John-ODell/Make_Music/hardware/review/final-package-20261009/before-corrections-REVIEW.md

# Final held-package review — 2026-10-09

Reviewed package commit d987896dbdd8cb6059bc102323f3ea0d89e263e1, root head23a23b6237898ece736c14430cfd86f4a77c5c58. The two later commits change checkpoint documentation; manufacturing payload and native CAD match the reviewed package. No repository/CAD/config writes, editor operations, exports, supplier contact/upload/order or merge occurred. Evidence was read from native exports and the source-bound recorded MCP results; no new live state or physical test is claimed.

## Verdict

No electrical, sourcing, placement or hash blocker was found. PR28 is suitable to merge **as a held review project after the ordinary package-presentation and parity-prose corrections below**. This is not a fabrication or upload release. Root owns corrections, regenerated manifest and merging.

## Verified

- All24 manifest input and65 output SHA256 values match; complete on-disk coverage is66 files including manifest. All17 native design/library hashes equal21b2108. Copies of README, assembly handoff and instrument-parts match their recorded inputs.
- Circuit contract and recorded IPC evidence agree on166 pads,48 values/full footprint IDs,65 footprints,38 connected nets and6 NC nets. U2 ten role/type assignments, power separation, cable/pull-up/bypass contracts and native MPNs pass. Identity sync is noop.
- Recorded saved/refilled all-severity ERC0, copper/layout DRC0, unconnected0; exactly4 reviewed metadata warnings, not suppressed. Native schematic parity count is4; electrical/net/value/full-ID discrepancy count is0. These are different categories.
- All47 purchased BOM refs/MPNs/values/footprints/datasheets match native XML. All47 native placement rows match recorded IPC x/y, rotation, side, value and footprint, including30 top SMT and17 THT with H1 underneath. Both derived placement tables agree. Five-unit sourcing fields and quantities expand exactly to235 carrier parts; optional bare carrier is separate.
- Generator diff from21b2108 changes only csv.DictWriter lineterminator to LF. A temporary quoted/comma/embedded-newline CSV round-trip passed; no CAD behavior change. Do not regenerate CAD to resolve these document issues.
- Package README, validation flags and visual-review scope preserve exact-part fit, long18650/holder/charger, final mechanical CAD, factory process and first-article/all-five bench holds. PM's actual Gerber/detail and five native drawing-page inspections are source-hashed recorded evidence; they were not visually rerun here.

## Corrections before final held-review merge

1. **Grouped connector descriptions (P2):** prepare_pcbway_review.py187 copies the first reference's functional Value into a group whose key excludes Value. In pcbway-bom-five.csv, J1/J2 are both labeled LEFT/Pico1–20 and J3–J14 all C4/GP16. Sourcing identities and per-reference carrier-bom are correct, but the group description falsely assigns one function to all references. Use a generic physical-part description for mixed-function groups, or split grouping by Value. Regenerate ordinary BOM/manifest and verify all235 quantities remain correct.
2. **Copied handoff links (P2):** copying assembly/PCBWAY_HANDOFF.md into the held package without rebasing its relative links breaks six required references: MODULE_HARNESSES.md, FIT_CHECKLIST.md, mechanical BUILD_READINESS, paper-fit PDF, power prototype-validation and budget worksheet. Adjust links for repository/package context or bundle companion review documents and validate final destinations. Preserve their hold language.
3. **Parity taxonomy (P2):** WORK_CHECKPOINT.md23 says unconnected/parity0, but native schematic_parity_issues is4. Replace misleading prose and add explicit classified counts if useful; retain the four exact native warning records. Do not change rules or native fields to make a zero claim.

Independent machine-check results, exact alias mismatches and broken-link destinations are in results.json; connectivity command output is in connectivity-output.txt. These findings were sent to PM. No current package hash is stale at the frozen audit snapshot; root's forthcoming document/package corrections require a new manifest.
