John-ODell/Make_Music/hardware/review/prequote-20261009/electrical/REVIEW.md

# Final electrical team review before quote — 2026-10-09

**ACCEPTED for quote-only review of five complete factory instruments**, plus optional sixth bare carrier. No actionable new electrical finding. This is not fabrication readiness or permission to order/upload. Root handles the authorized quotation workflow.

Scope: root checkout `/Users/johnodell/Desktop/Make_Music`, exact merged commit07f0e03b4d69f809a0e0871b89afc9e052754bba. All17 native source/library hashes match21b2108 before/after; source snapshots are retained. Reviewed current package exports and source-bound recorded MCP evidence. No repository/CAD/library/config changes, sync, refill, GUI operation, export, supplier contact or upload occurred.

Fresh saved-file Konnect13.0/KiCad10.0.6 checks completed: full-severity ERC0; layout/copper DRC0; unconnected0; exactly4 retained native metadata parity warnings. C17/C18 missing Header and J1/J2 missing MPN descriptions/UUIDs exactly match the reviewed native records. No hidden category, truncation, rule suppression or metadata substitution. Fresh DRC explicitly reports saved_file, live_board_synced=false, zones_refilled=false. These checks do not claim a newly saved/refilled or freshly inspected live GUI state.

All166 source-bound recorded IPC pad nets,48 values/full footprint IDs and identity-sync noop agree with native XML. Circuit verifier checks38 connected nets/6 NC nets, all41 typed power endpoints, ten U2 terminals/no pad11, fused switched battery path and D2/D3 polarity, and separation of VBUS/battery/VSYS/3V3. All40 Pico socket physical positions/GPIO assignments use the previously independently verified unchanged mapping: J1.n=Pico n; J2.n=Pico n+20. Notes GP16–22/26, left semitone/octave GP27/28, J13/J14 signals GP13/12, and free GPIO0–11/14/15 remain correct.

Unchanged firmware uses both GP12/13 channels at the same frequency, HIGH idle for active-low ST0238, and per-touch active-level configuration. Existing host tests/mapping/circuit checker are unchanged from the reviewed revision; no redundant firmware test rerun or new hardware-performance claim. R1/R2 reset pull-ups and C11/C12/C17/C18 supply bypasses match the circuit. Carrier contact order1SIG/2regulated3V3/3GND requires the documented ST0238 GND/I/O/VCC permutation; actual module-end labels, polarity/momentary configuration and reset/sound behavior remain delivered-part/bench gates.

All47 native placements match recorded IPC x/y/rotation/side/value/footprint; correct BOM/functional descriptions cover47 unique purchased references and235 parts for five. Thirty top SMT/17THT with H1 beneath. Current assembly tables and electrical evidence are byte-identical to the accepted follow-up. Native parity4 remains separate from electrical discrepancy0. No sourcing/placement mismatch was found.

Exact Pico/socket/module/cell/holder fit, protected P1835J lot/terminal limits, L1 charger pairing hold, contact/crimp ampacity, final fixture/cassette CAD, factory land/stencil/annular-ring/panel/orientation acceptance, first-article/all-five bench and source-isolation/UVLO/fault/thermal tests remain open. Quote-only acceptance permits pricing/metrology/process discussion; it waives none of those release gates.

Results and full raw responses are in this directory. Review complete; idle after handoff.
