John-ODell/Make_Music/hardware/review/prequote-20261009/power/REVIEW.md

# Final power review for conditional quotation — 2026-10-09

Reviewed merged commit **07f0e03b4d69f809a0e0871b89afc9e052754bba** read-only. **Conditionally accepted for quote review; not ready for hardware fabrication.** No CAD/document/repository changes, new editor checks, supplier contact or upload were performed. All files produced by this helper are in this temporary review directory.

## Evidence checked

- Frozen merged packet inputs: **61 input hashes and 43 support-input hashes pass**, covering 63 unique source files. **109 packet output hashes**, all **17 native source hashes** across three matching source checkpoints and **128 package-local links** pass. Current rear-edge XML/ERC/DRC/live-board records match the packet copies. These are saved/source-bound evidence checks, not a new live ERC/DRC run.
- Recorded connectivity/board verification passes: **166 physical endpoints /48 electrical parts /41 power endpoints**, all pad nets/values/full footprint IDs agree; identity synchronization is a no-op. ERC0, copper/layout DRC0 and unconnected0; **four exact metadata/parity warnings remain**, so overall DRC/parity is not zero.
- All **47 purchased carrier references** match native MPN/value/footprint and recorded X/Y/rotation/side. **31 grouped sourcing rows /235 parts for five**, **30 top SMT /17 THT per carrier**, only **H1 bottom**; the SMT and manual-THT placement tables have exact coverage/coordinates.
- Exact power parts and orientation contract agree: **TPS259474LRPWR** U2 (ten terminals, IN5/OUT6, no pad11), **3403.0275.23** F1 upstream, **MN12SS1W03** S1 (common2/ON3/OFF1 NC), **SS14-E3/61T** D2 shunt K1 VSYS/A2 GND, **SMAJ5.0CA** D3 bidirectional input TVS, **B2B-PH-K-S(LF)(SN)** H1 positive1/GND2. No carrier series D1. USB uses the unmodified Pico's onboard diode; no raw-cell/USB connection to 3V3/GPIO. USB powers the instrument with S1 OFF, does not charge the cell and bypasses the battery F1/U2 protection.
- C17/C18 are **C2012X7R1A106K125AC**, 10µF each on regulated3V3/GND, retaining twelve100nF bypasses. C13/C14/C16 are **C2012X7R1E475K125AB** and C15 **C1608C0G1H103J080AA**. Main nominal VSYS subtotal remains56.4µF, separate from the additional20µF on3V3. Effective capacitance and startup remain unmeasured. Limits remain0.70A battery input,250mA external/350mA total3V3 and100µF maximum VSYS; the515mA low-voltage sizing example is not a measured load or runtime guarantee.

## Quote-document disposition

The merged07f0e03 request compared complete, SMT-only and bare routes. The newly authorized middle route must be **five carriers with all47 purchased parts soldered**, including all17THT parts and bottomH1: **150SMT +85THT parts for five**. Pico/modules/cell/holder/harness/mechanics/final instrument tests are explicit exclusions or separate lines for this middle route. SMT-only may remain an additional breakdown. These are alternatives for the same physical design, not fifteen ordered boards. The optional sixth bare keepsake is additional.

During the read-only audit, PM began that authorized ordinary-document update. Root HEAD remained 07f0e03, but live `hardware/assembly/QUOTE_REQUEST.md` changed; its **two manifest input entries differ** from the old packet. Its frozen 07f0e03 blob matches both recorded hashes. The observed new draft correctly adds the three requested alternatives and maintains quote-only authorization/production holds. PM subsequently updated `ASSEMBLY_BUDGET.md` with the same all-47 carrier option; the ordinary-document correction is complete in those live drafts. **Regenerate the coherent quote packet and manifest after final ordinary-document edits, then verify all inputs/outputs before quote submission.** This is expected document staleness during PM work, not a circuit-source defect. `packet-checks.json` retains the two live differences seen at that earlier instant; later budget edits add another input change. `frozen-input-checks.json` records the all-pass merged baseline.

## Remaining fabrication and first-article requirements

No new actionable circuit discrepancy was found within this source/export review. The following existing gates remain material and must accompany a conditional quote:

- Delivered **P1835J opposite-end button-top** identity, current-lot charge/discharge/PCM thresholds/recovery and measured holder fit/removal/retention. Published planning dimensions do not prove the exact variant fits.
- **External charger compatibility HOLD:** L1's4.242V upper tolerance exceeds the cell page's unqualified4.20V maximum. Selecting500mA or a shared brand does not approve pairing. Require current-lot CC/CV voltage/current/termination/temperature limits, accepted charger revision/tolerances/recovery and bay fit. One shared5V1A supply/cable/charger set is only a quote assumption; no approved pair or exact input-supply SKU exists.
- **BH-18650-W** contact/holder capability for0.70A normal and≥1.2A continuous branch; included factory24AWG TR64 leads150±5mm each, no duplicate wire purchase. Measure insulation OD against JST **0.8–1.5mm** and qualify **PHR-2 /SPH-002T-P0.5S** strip/tool/crimp, continuity, polarity, service bends and strain relief. Wire color and supplied stripped length are not qualification.
- Final measured/toleranced cassette/retention/support drawings and≥2mm loaded clearance; nominal112×36×44mm cassette and≥47mm supports remain proposals. Factory acceptance of U2 mask/stencil, capacitor lands, socket annular rings, panel rails/fiducials, orientation and handling remains open.
- Current-limited emulator bring-up before a real cell: measured load/current/thermal/startup, UVLO/restart, fault latch/reset/reversal/isolation, effective capacitors and switch low-load endurance. Separate USB source/inrush/fault qualification is required because USB bypasses F1/U2. Measured module operation/current and actual touch configuration remain pending.
- **First article within the five**, followed by separate acceptance records for **all five**; the optional bare board receives no populated-component allocation. No physical fit, bench result, supplier acceptance, price or fabrication release is claimed.

The packet's physical-fit, bench, supplier-acceptance and fabrication-release flags are all false. Conditional quote review may proceed after PM's coherent quote-document/package refresh; fabrication or first-article assembly requires its separate release gate.
