John-ODell/Make_Music/hardware/manufacturing/REVIEW_ONLY_DO_NOT_ORDER/support/hardware/mechanical/MODULE_FIXTURE.md

# Raised module fixture — dimensioned prototype proposal

Updated 2026-10-09 for the corrected 18650 cassette; upper-fixture geometry was reviewed 2026-10-08. Propose one machined **unfilled acetal insulating plate**, open-backed seats, and removable insulating edge keepers for all ten touch boards and both ST0238 boards. Nothing passes through a module's undocumented mounting holes. Module wiring uses flexible, factory-installed leads; headers and solder joints carry no playing load. This is an engineering fixture proposal, **not verified actual-part fit, a strength certification, or manufacturing CAD**.

The editable [plan and detail drawing](module-fixture-plan.svg) and [carrier attachment CSV](fixture-mounting.csv) define the proposal. PM owns PCB edits. Dimensions retain the legacy carrier service datum native (20,20): local (0,0), x right, y forward, millimetres. The PM's KiCad offset adds (20,20); both coordinate sets are in the CSV. For the proposed 330 x121.5 carrier the new physical rear edge is legacy y=-1.5/native y18.5, while every fixture/body/mount coordinate stays fixed. DATUMS.md distinguishes the physical upper-left from this retained service origin. z=0 is the carrier **top** surface, unlike the cassette document's underside z convention. Selected delivery is five complete instruments and an optional sixth bare carrier; the [physical-fit checklist](PHYSICAL_FIT_CHECKLIST.md) assigns metrology/assembly to the assembler and paper-fit/reach to the user.

## Geometry and fixed carrier interface

Plate perimeter polygon, in order: **(2,36), (42,36), (42,56), (120,56), (120,68), (326,68), (326,119), (2,119)**. Bounding size 324 x 83. Main plate thickness **4 mm**, raised on **24 mm** custom insulating spacers (OD8, ID3.2), giving a module support plane z=28. Machine integral 1 mm-high locating fence segments from a 5 mm blank; main plate/fastener seats remain 4 mm thick. Stock material, machining radii, flatness and tolerances need fabricator agreement. Do not use carbon-filled plastic or conductive coatings.

Nine **3.2 mm NPTH carrier and plate holes**, with **8 mm diameter copper/component keepouts on both carrier faces**:

| ID | Mechanical (x,y) | KiCad (x,y) |
|---|---|---|
| F1 | (8,74) | (28,94) |
| F2 | (45,83) | (65,103) |
| F3 | (50,114) | (70,134) |
| F4 | (155,114) | (175,134) |
| F5 | (257,114) | (277,134) |
| F6 | (291,114) | (311,134) |
| F7 | (155,73) | (175,93) |
| F8 | (189,73) | (209,93) |
| F9 | (291,73) | (311,93) |

These are additional to the four corner supports and four cassette mounts; do not share bolts with the removable cassette. Plate-only 8 mm tool-access openings at the two existing front carrier supports (6,114) and (324,114) preserve access; the right opening forms an edge notch. No extra carrier holes are required for these openings. The minimum fixture attachment centre-to-plate-edge distance is 5 mm, leaving at least 1 mm beyond the 4 mm keepout radius.

## Twelve seats and removable keepers

| Boards | Centre coordinates | Nominal PCB body | Proposed seat opening / corner ledges |
|---|---|---|---|
| Eight notes C4..C5 | x=70,104,138,172,206,240,274,308; y=94 | 24 x 24, user reference | 24.6 x 24.6, with four integral 3 x 3 corner tabs retained in that opening |
| Semitone / octave | (24,54), (24,94) | 24 x 24, user reference | Same touch seat |
| Buzzer 1 / 2 | **(60,67.5), (98,67.5)** | 32 x 14, ST0238 listing | 32.6 x 14.6, with four integral 5 x 3 corner tabs |

The buzzer bodies move 1 mm left and 4.5 mm forward from the earlier body reservation, independently of the PM's fixed headers (61,49)/(99,49). Flexible leads bridge that offset. Body centres are not header pin coordinates. All touch centres, ascending order and left-hand modifiers remain fixed. Touch body gap remains 10 mm; fences extend the fixture width to 28 mm, leaving **6 mm between raised fence envelopes** at 34 mm pitch. Keeper hardware is concentrated along rear/front edges. Validate the assembled finger gap and reach; do not describe the complete fixture as having an unobstructed 10 mm gap.

For each touch seat, two diagonally opposed 2.2 mm **plate-only** keeper holes have local offsets **(-9.5,+14), (+9.5,-14)** from the module centre. Four underside corner tabs remain; the two keepers retain uplift rather than pressing every corner. Rock/lift and load trials remain necessary. Each stepped keeper is 6 mm wide x 6 mm deep x 1.5 mm upper thickness. Front keeper bounds are x=hole_x±3, y=centre_y+10.5..+16.5; rear is mirrored. Its underside pedestal occupies only y outside the seat boundary (|local y|≥12.3), with height **t**, the measured PCB thickness. This hard stop prevents screw tightening from bending the PCB. The overhang contacts nominal bare top-edge lands 5.5 x 1.5 near each corner; underside tabs overlap the nominal board by 2.7 x 2.7. Both contact regions must be free of pads, traces, components and electrode area on the actual module. Initial t=1.6 is a **shim/stack assumption**, not a measured module thickness.

For each buzzer, the two diagonal keeper hole offsets are **(-11,+9), (+11,-9)**; keepers are again 6 x 6 x 1.5 above measured t. Front bounds are x=hole_x±3, y=centre_y+5.5..+11.5; rear mirrored. Pedestals stay outside |local y|≥7.3. The wider corner ledges provide support beneath these keepers. Nominal bare top-edge contact is 6 x 1.5, with support overlap at least 2.7 x 1.5. Keepers avoid the centre sound opening; its actual position, diameter and height must still be checked. Do not clamp the sound can, header, components or solder joints.

Fence segments are 1.7 mm wide, 3 mm long, 1 mm high. East/west sides each have two segments at along-edge offsets ±7.5 for touch seats, ±3.5 for buzzers. Add a rear/north fence at local x=-7.5 for touch (-9 for buzzer), and a front/south fence at x=+7.5 (+9 for buzzer), on the **two corners without keepers**. These six segments restrain all four directions and avoid the keeper pedestals. They locate PCB edges with 0.3 mm nominal per-side clearance. Central north/south wiring remains open; its actual width depends on fence/header geometry. **Actual headers may require relocating fence segments or adding a wire notch.** Keep four-direction restraint and both diagonal keepers; do not remove a necessary stop and rely on friction. Window/ledge/keeper positions can be revised within the fixture without changing the nine carrier mounts.

## Clearance against the current carrier

Checked against the saved placement export at master `6155ca0` and the PM's 2026-10-08 correction: move only J3/C4 and J4/D4 from mechanical y75 to **y78**, keeping x and rotation. Their pad1 coordinates become (67.46,78)/(101.46,78), native KiCad (87.46,98)/(121.46,98); their header body centres are (70,78)/(104,78). The other six note headers remain at their note x, y75. Modifier headers remain (24,35)/(24,75), buzzer headers (61,49)/(99,49), J15 pad1 (50,12), power reservation x216..264,y44..68, switch centre (250,55), and underside H1 pad1(269,20), native(289,40), as confirmed in the held root 806457b IPC inventory. H1 is bottom/0 degrees; the earlier (229,20) placement is historical. This held-export inspection is not a fresh live readback or a fitted lead/service-access pass. PM's earlier J3/J4 native check predates the H1 move. The later held 806457b inventory was inspected separately for H1/mount geometry; this drawing makes no fresh native DRC, electrical parity or physical-fit claim. See [build-readiness audit](BUILD_READINESS.md) for exact cap/keeper spacing and socket edge assessment. For conservative plan checks, reserve ±6 x ±4 around each module-header centre; this is a planning envelope, not a verified header body or pad1 convention. Expansion access is reserved x45..58,y8..55.1 (last pin y50.1 plus 5 mm). Pico/removal access extends to x104.5..135.5,y56; the fixture rear tongue starts at y56. All contacts with that service boundary are nominal and need actual tolerance/access checks.

Fixture holes and their 8 mm keepouts clear these reservations, the ten **26 x 26 touch-body copper keepouts**, both nominal buzzer bodies, revised 18650 cassette x145..257,y12..48 and its four bolts, proposed relocated H1 access x265..275/y15..27, and the corner supports. The new cassette/≥47 mm lower supports need independent measured CAD/load acceptance; the four carrier cassette mounts stay fixed with a lowered holder platform. See [18650 handoff](WIRED_HOLDER_PROPOSAL.md). The corrected J3/J4 bare header bodies clear the nominal buzzer bodies by **2.23 mm** in y; their broader ±6 x ±4 service boxes still overlap the buzzer plan projection by 0.5 mm. That service allowance must fit vertically, and the tabs stay intact. C1/C2 remain at (76.46,75)/(110.46,75); their courtyards partly overlap the buzzer/ledge plan projection, but the exact KEMET body is at most 0.95 mm tall beneath the z24 plate. No cap move is needed for the nominal mechanical assembly. Proposed note-cable corridors run forward at x67..73 and x101..107 beneath the plate, away from the rear touch keepers and caps; actual module-end header positions still determine the final route.

PM’s merged carrier interface specifies Harwin M20-999 headers with 2.54 mm insulator + 6.1 mm mating post = **8.64 mm nominal bare height**, before a female housing. The manufacturer-supported **candidate carrier cable end** is M20-1060300 housing with three M20-1180046 tin contacts; its 14 mm housing gives a **16.54 mm nominal rigid stack**, plus any mating gap. Its 5.5..6.3 mm allowed mating post range contains the nominal 6.1 mm post; check actual post/gap tolerances. This identifies a candidate, not an approved harness or module-end connector. Reserve **18 mm total** for housing, joints and dressed wires as the existing engineering envelope. Only 1.46 mm nominal remains beyond this housing, so wire selection, bend radius and actual total height cannot be signed off from the connector drawing. The [audit](BUILD_READINESS.md) records wire/contact limits and the clearance equation. Increase spacer height or choose a verified lower cable end if the measured dressed assembly fails; recheck screw length and finger height. Lift the removable fixture to mate/service covered headers; provide measured service-loop slack and strain relief without loops entering touch windows or the battery. Do not force a tall plug beneath the fixture.

At z=28, provisional module underside projection 6 mm, carrier mated-header/component envelope 18 mm, and fixture deflection allowance 0.5 mm leave **28−6−18−0.5 = 3.5 mm** before dimensional tolerances. Require at least **2 mm measured remaining clearance** after tolerance/deflection, including fastener tips, joints and wires. Increase spacers or relocate hardware if it fails. The quoted touch-board 7.2 mm overall height is not an underside projection or an enclosure stack. Actual buzzer height and total top enclosure height remain unmeasured. First-prototype Pico candidate is **Raspberry Pi Pico H SC0917**, with manufacturer-installed male headers, per PM selection and the official [Pico datasheet](https://datasheets.raspberrypi.com/pico/pico-datasheet.pdf) ordering table (local release21). The Samtec SSQ socket engagement, header/body height and plug/removal clearance remain actual-part fit checks; Pico 2 is not the current prototype candidate. Plate geometry leaves Pico, USB/BOOTSEL and vertical GPIO access open; verify with plugs fitted and during upward Pico removal.

## Hardware and factory assembly

Candidate natural nylon 6/6 hardware is documented in the [Essentra manufacturer catalog](https://essentracomponents.bynder.com/m/6e2e9b888468b393/original/2685970-pdf.pdf), visually checked at printed pp146,182,183,197 (PDF pp35,71,72,86). Material ratings apply to catalog parts, not the custom plate or whole instrument.

| Qty | Candidate | Source dimensions / purpose |
|---|---|---|
| 9 | 50M030050P035 | M3x0.5, 35 mm screw; head Ø5.3..5.6, height2.2..2.4; p146 |
| 9 | 04M030050HNDIN34814 | M3 nut, flats5.3..5.5, height2.2..2.4; p183 |
| 18 | MFW030A | M3 washer, ID3.2 OD7 thickness0.5; p197 |
| 9 | Custom acetal spacer | Proposed OD8 ID3.2 length24; dimensional design, not a sourced MPN |
| 24 | 50M020040P010 | M2x0.4, 10 mm keeper screw; headØ3.7..4.0, height1.4..1.6; p146 |
| 24 | 04M020040HN | M2 nut, nominal flats3.9, height1.2; p182; no locking feature or tolerance inferred |
| 48 | MFW010A | M2 washer, ID2.2 OD5 thickness0.3; p197 (MFW020A is for M2.5 and is not selected) |
| 20 + 4 | Custom stepped keepers | Touch + buzzer; thickness t+1.5 with relieved underside; exact t measured per lot |

M3 stack under the screw head: 0.5 washer + 4 plate + 24 spacer + 1.6 carrier + 0.5 washer + nut max2.4 = **33 mm**; M3x35 leaves nominal 2 mm beyond nut. M2 stack at assumed t=1.6: 0.3 washer + 1.5 keeper + 1.6 pedestal + 4 plate + 0.3 washer + nominal1.2 nut = **8.9 mm**; M2x10 leaves nominal1.1. Recheck actual tolerances, thread engagement, tool access and tip clearance; select another length if needed. No torque, pullout strength or long-term creep claim is made.

Factory scope per instrument includes machining/deburring/cleaning the plate, spacers and keepers; actual-module metrology and fixture fit; mounting the plate; installing all 12 modules and 24 keepers; making, labeling and testing 12 flexible harnesses; and retention/functional inspection. Quote this work for five complete instruments; qualify the first within those five before repeating the accepted build. The optional sixth bare keepsake requires no fixture/modules. The prototype uses two diagonal keepers per board to reduce labor. **Machined acetal, custom measured-thickness keepers and manual fixture assembly are cost drivers** requiring a separately priced mechanical subassembly. After actual-part metrology, compare a simpler measured-hole/standoff mount if the modules have usable, documented mounting holes; that future alternative is not approved by this proposal. Partial assembly is a budget comparison, not the selected deliverable. Do not transfer keeper fitting, soldering or crimping to the user by omission. Final removable Pico/cell insertion and delivery instructions must follow assembler qualification; no precision equipment is assumed for the user. No vendor contact, orders or sourcing acceptance occurred.

Factory sequence: populate/inspect carrier with Pico and cell absent; trial-fit measured modules and dummy boards in the fixture offline; install the nine spacers/plate without bowing carrier; place modules face/sound opening up; tighten keepers to their measured pedestal stops using supplier guidance; dress short service loops below windows with separate insulating strain relief and no wire pinch; continuity/polarity-check each harness against the actual module labels; connect and verify all inputs/buzzers. Do not infer signal order from a photograph or from the provisional schematic. Mount/module harnesses remain removable for service.

## Fit and release requirements

1. Measure all board outlines, thicknesses, underside/top components, headers, electrode/sound locations and both-face bare support lands. If proposed tabs/keepers touch circuitry or active surfaces, revise that seat before manufacture. Never drill or bend the modules to fit.
2. Verify nine mounts, spacers, tip and cable clearances, corner-support tool openings, cassette removal, switch/GPIO access and upward Pico removal on the complete assembly. Machine-seat clearances/flatness/tolerances are not released by this drawing.
3. Before playing, check retention, lift/tilt and rocking about the diagonal keeper axis, and verify loaded clearance/no contact with the carrier. The optional dummy-board qualification targets are 10 N downward per seat and 20 N distributed across several touch seats, ≤0.5 mm deflection, no permanent set or release. These are proposed characterization targets, not a manufacturer requirement or a certified real-module force rating; they need not be completed to request a quote or make a bare carrier. Extended service/creep trials may inform future refinements; they are not a prerequisite to repeating the accepted first-instrument build within the five. The ≥2 mm measured clearance and secure support requirements remain mandatory for each assembled instrument.
4. With actual modules fitted, test finger access, rapid notes, held left modifiers, neighbor false triggers, powered idle/recalibration and USB/battery behavior; compare before/after fixture installation. Insulating plastic does not guarantee unchanged capacitive response. Confirm sound openings and loudness.

Validation: three SVGs parsed and were rendered/visually checked. All nine fixture keepout circles fit inside the plate and clear the cassette/corner holes, conservative header boxes, power/Pico/J15 reservations, touch-body keepouts, buzzer bodies and proposed keepers. The 24 keeper envelopes do not intersect each other. CSV origin offsets, 33/8.9 mm nominal fastening stacks and 3.5 mm nominal component clearance were checked. Manufacturer fastener sheets and the Pico H ordering-table entry were inspected. No physical module/fixture test, PCB DRC, manufacturing approval or final fit claim is made.
