John-ODell/Make_Music/hardware/manufacturing/REVIEW_ONLY_DO_NOT_ORDER/support/hardware/power/pcbway-readiness.md

# PCBWay power and assembly readiness audit

**2026-10-09 status:** this is historical evidence for the explicitly dated **18350** checkpoint below. The user has corrected the intended cell to protected **18650**; see [the current handoff](18650-handoff.md). Original audit results and counts are preserved. They do not claim a review of the new holder/cassette, PM's header changes or C17/C18 integration.

Reviewed 2026-10-08 at fetched `origin/master` **6155ca0**. **Release verdict: INCOMPLETE.** No concrete electrical topology defect was found in the audited power block; this does not establish tested hardware or an accepted production package. PM owns CAD changes, final package generation and integration.

Rechecked fetched master **3af4ace** before submitting this report: its changes since the audited baseline are schematic-review documentation only; the audited CAD and held manufacturing files are identical. PM's subsequent live header changes and any adopted capacitor additions require a fresh final package/checkpoint.

User's updated order preference: **five fully assembled instruments**, with an **optional sixth bare carrier as a keepsake**. Quote all five populated carriers, including small SMT components and all THT connectors/switches, plus harness/module installation and mechanical assembly. Pico and protected-cell fitting follow the agreed acceptance procedure; describe any supplier exclusion explicitly rather than assuming user soldering. The optional bare board is additional to the five complete instruments. No actual parts are available for fit measurements yet.

## Evidence obtained

- Fresh native KiCad 10.0.6 configured root ERC: zero violations; the project's existing ignored check categories were retained, with no new exceptions added. Complete-board DRC with schematic parity: zero violations, unconnected items and parity issues. No pcbnew/SWIG or CAD editor was used.
- Fresh exported XML passes the carrier contract: 46 physical components, 162 endpoints, all 41 power endpoints and R3–R8/C13–C16 mapping. Purchased carrier BOM has 45 references, every MPN present; all 45 match the held position file. TP1 is bare copper and excluded from purchased parts.
- Held manifest: all 21 input and 20 output SHA-256 entries match non-empty files. This proves package consistency, not Gerber-viewer or vendor placement acceptance.
- Konnect meta-tools loaded the requested audit toolsets, but those loaded handlers were not callable in this session. Native CLI/export evidence above is the basis of this audit; no Konnect aggregate/manufacturing verdict is claimed.

Selected power is protected **P1835C2**, offboard **Keystone 1101/JST-PH** harness, upstream **3403.0275.23 1.25 A fuse**, **MN12SS1W03** switch and **TPS259474LRPWR** eFuse. H1.1→F1→S1 common2/ON3→U2 IN5; OUT6→Pico physical39/VSYS. U2 GND8/PGTH4 are grounded; PG3/ITIMER10 are intentional NC. D2 **SS14-E3/61T** is a shunt, cathode at VSYS. D3 is bidirectional **SMAJ5.0CA**. The ten-contact RPW footprint has no ground pad11. VBUS40, VSYS39 and regulated 3V3 pin36 are distinct; carrier D1 is removed. Pico's onboard USB diode remains. USB does not charge the cell and powers the instrument with the battery switch OFF.

Nominal calculations agree with the [TI datasheet](https://www.ti.com/lit/ds/symlink/tps25947.pdf): UVLO 3.221 V OFF/3.546 V restart, OVLO 4.995 V trip/4.537 V recovery at **U2 IN**, and approximately 1 A breaker with 3.32 kΩ. Published current extrema use VIN=12 V; 1S trip behavior remains a bench qualification. Input C13 is 4.7 µF; output C14/C16 total 9.4 µF nominal; C15 is the 10 nF DVDT capacitor with 100 Ω series damping. Verify effective output capacitance >1 µF and total VSYS ≤100 µF. Local routes/footprint geometry retain the previously reviewed circuit; current parity does not establish solder-process approval.

## Bulk capacitance and review heuristics

The selected original Pico H includes the original Pico regulator circuit. The [official Pico datasheet](https://datasheets.raspberrypi.com/pico/pico-datasheet.pdf), Appendix B Figure 19 (Rev3 schematic), shows **RT6150B-33GQW with 47 µF at VSYS input and 47 µF at 3V3 output**, each 6.3 V X5R. The [Richtek datasheet](https://www.richtek.com/assets/product_file/RT6150A=RT6150B/DS6150AB-06.pdf), page 10, recommends a minimum 10 µF output ceramic, near VOUT/GND, and describes larger capacitance as reducing ripple and load-step voltage drop. Thus the carrier-only “no ≥10 µF 3V3 bulk” heuristic does not demonstrate a missing regulator capacitor. Nominal values do not establish effective capacitance under bias or transient compliance.

**PM CAD recommendation before final export:** add one **10 µF ceramic from 3V3_OUT to GND beside each buzzer header J13/J14**, retaining existing 100 nF bypass. Exact candidate: [TDK C2012X7R1A106K125AC](https://product.tdk.com/en/search/capacitor/ceramic/mlcc/info?part_no=C2012X7R1A106K125AC), 10 µF ±10%, 10 V, X7R, 0805, 1.25 mm nominal thickness; check the manufacturer's land guidance. This modest addition is warranted as a precaution for two pulsed loads fed over the carrier and cables. It is not a substitute for adequate regulator current or module-end bypass, and 10 µF is a starting value, not a demonstrated requirement. Check [TDK's bias/temperature characterization](https://product.tdk.com/en/system/files/dam/doc/product/capacitor/ceramic/mlcc/charasheet/c2012x7r1a106k125ac.pdf) and qualify startup/ringing/transients. The additional 20 µF is on **3V3**, not the ≤100 µF VSYS node; it still contributes to regulator startup demand. No CAD change is made in this audit. If adopted, regenerate checks, BOM, SMT centroid and manifest; baseline counts below will increase by two SMT capacitors.

For each touch board, [Tontek's application circuit](https://www.tontek.com.tw/uploads/product/243/TTP223-BA6_V2.1_EN.pdf), page 6 of 8, requires 100 nF close to IC VDD/VSS. Carrier C1–C12 are before the cables. Inspect actual module-end decoupling and add it to the module/harness assembly scope if absent. Scope at the modules during simultaneous buzzer pulses, touch LED transitions and source changes; required load/current/ripple evidence is still missing.

TP1 is a bare VBUS test pad and adds no active load requiring its own bypass capacitor. Pico already has the VBUS-to-VSYS diode/regulator-input network. A dedicated carrier 3V3 test point would help factory probing, but existing 3V3/GND header contacts provide measurement access; absence of a dedicated pad is not a connection defect. H1 is bottom-side **THT**, so the dual-SMT-assembly warning does not apply. These dispositions address the reported review heuristics; they do not claim that this helper executed the PM's live Konnect review.

## Concrete package correction for PM

The held `carrier-positions.csv` includes **28 top SMT and 17 THT** references. [PCBWay's file requirements](https://www.pcbway.com/assembly-file-requirements.html) specify an SMT-only centroid. Generate a **28-row top SMT centroid** and keep the 17 THT locations in a separate manual assembly map. Preserve bottom-left origin, mm, x-right/y-up and current rotation values; confirm U2 pin1/D2 cathode in the assembler placement review. H1 is bottom THT, not bottom SMT. Include all 45 purchased carrier parts in the BOM, with quantity, exact manufacturer/MPN and assembly type. Do not omit THT from the BOM when filtering the centroid.

The THT set is J1–J15, S1 and H1. Supply both-side drawings and a socket alignment jig instruction; Pico H **SC0917** stays removable. Mark H1 circuit1 positive/circuit2 GND on underside assembly and harness drawings. Label cell/charger/Pico/modules as separate instrument items, not SMT placements. Socket engagement at 17.78 mm row spacing and actual module-end cable pin order remain cold-fit checks.

## Acceptance evidence still required

1. **Order/process:** supplier acceptance/pricing for five complete instruments and the optional sixth bare board, finish, agreed stackup with ≥35 µm finished copper on each layer, component procurement/population and a complete mixed-assembly scope. PCBWay documents [SMT, THT, cable and electromechanical services](https://www.pcbway.com/pcb-assembly.html); this does not prove acceptance of our custom fixture or cassette. Agree panel rails/fiducials/tooling: its [panel guidance](https://www.pcbway.com/pcb_prototype/Panel_Requirements_for_Assembly.html) describes three panel fiducials; no accepted panel/rail design is in this held package. Obtain process acceptance for U2's 0.20 mm pad gap, nominal 0.10 mm mask web and TI 0.100 mm example stencil, plus inspected Gerber/drill and placement previews.
2. **Mechanical/manual scope:** measured Pico/socket stack; protected-cell/1101 travel, retention and contact ampacity; exact module headers/support lands; final cassette, fixture, keepers and feet manufacturing CAD/tolerances. Include crimp/solder/insulation, strain relief, polarity continuity, fastener stack and inspection instructions. The dimensioned proposals are not machining files.
3. **Cell/charger:** L1 at **500 mA** only remains a candidate. Its [manual](https://www.tme.eu/Document/f545a63a03e51e3b3ea513f2f0317887/L1_KeepPower_EN.pdf) permits 4.2 V±1%, up to 4.242 V; the current [cell page](https://www.keeppower.com.cn/products_detail.php?id=566) says 4.20 V maximum. Resolve current-lot voltage/current limits, termination, temperature handling, PCM recovery and bay fit as recorded in rev1-handoff.md. Carrier protection is not an external charger qualification.
4. **Electrical/function:** execute [prototype-validation.md](prototype-validation.md), retaining its blank record until measured. Qualify USB/battery reversal and transients, 1S fault/latch/reset dwell, UVLO rebound, rail voltage/thermal behavior, module function and switch low-load endurance. No real cell is fitted before polarity/load checks pass.
5. **Load margins:** [SunFounder ST0238](https://www.sunfounder.com/products/3-3-5v-passive-low-level-trigger-buzzer-alarm-sound-module) supports 3.3 V and a PNP low-trigger input but gives no module current or input-threshold guarantee. [Tontek](https://www.tontek.com.tw/uploads/product/243/TTP223-BA6_V2.1_EN.pdf) specifies bare-IC no-load current at 3 V, excluding the reference board LED/configuration resistors. Measure both complete module types. Enforce ≤250 mA external, ≤350 mA total 3V3 and ≤0.70 A battery input, with simultaneous startup/LED/buzzer/expansion peaks; see current-budget.md. Provide HIGH buzzer idle/reset and verified momentary touch polarity in firmware. A source change may reboot; stop playing before changing it.

These are package/process and prototype-acceptance holds. They are not measured failures or evidence that the verified connection contract is defective. No supplier contact, purchase, upload or manufacturing release occurred in this audit.
