John-ODell/Make_Music/hardware/manufacturing/REVIEW_ONLY_DO_NOT_ORDER/support/hardware/mechanical/cassette-18650-geometry.csv

item | coordinate_frame | x_mm | y_mm | width_mm | depth_mm | z_min_mm | z_max_mm | status
cassette_outer_min | mechanical_top_view | 145 | 12 | 112 | 36 | 0 | 44 | engineering_proposal_not_machining_release
BATTERY_CASSETTE_18650_REVIEW | native_KiCad | 165 | 32 | 112 | 36 | 0 | 44 | mechanical_reservation_not_blanket_copper_keepout
holder_body_nominal_min | mechanical_top_view | 162.15 | 19.55 | 77.70 | 20.90 | 16 | 37.31 | primary_MPD_rev_G_body_not_fitted_cell
holder_body_tolerance_min | mechanical_top_view | 161.90 | 19.30 | 78.20 | 21.40 | 16 | 37.81 | body_only_maxima_fitted_stack_pending
BH18650W_BODY_MAX_REVIEW | native_KiCad | 181.90 | 39.30 | 78.20 | 21.40 | 16 | 37.81 | body_only_mechanical_reservation_actual_fitted_stack_pending
holder_wire_retainer_region_min | mechanical_top_view | 154 | 17 | 94 | 26 | 14 | 40 | planning_allowance_actual_bend_pending
carrier_mount_1_retained | mechanical_top_view | 150 | 17 | 3.2 | 3.2 |  |  | existing_NPTH_keepout_diameter_8
carrier_mount_2_retained | mechanical_top_view | 210 | 17 | 3.2 | 3.2 |  |  | existing_NPTH_keepout_diameter_8
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
